lukejiang9020/solartrackers/imgs/basic_diagram.png

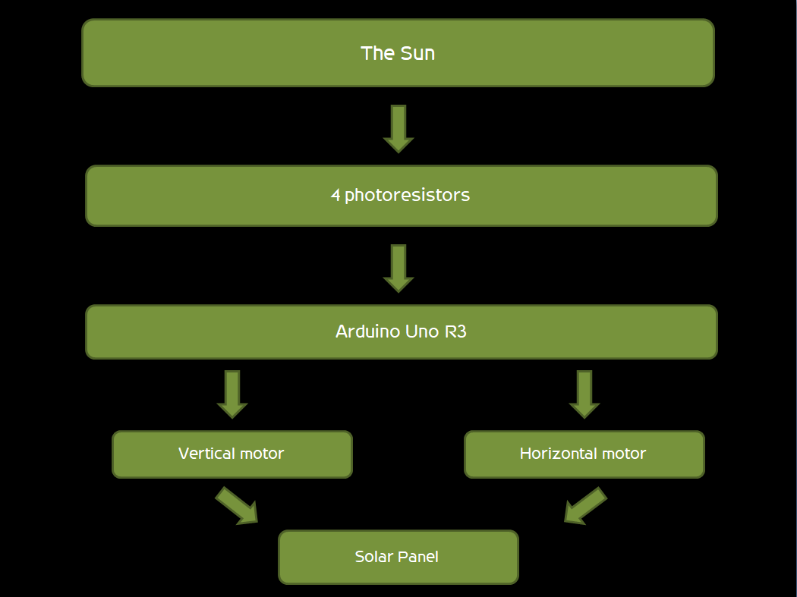
imgs/basic_diagram.png
