lukejiang9020/solartrackers/imgs/circuit_diagram.png

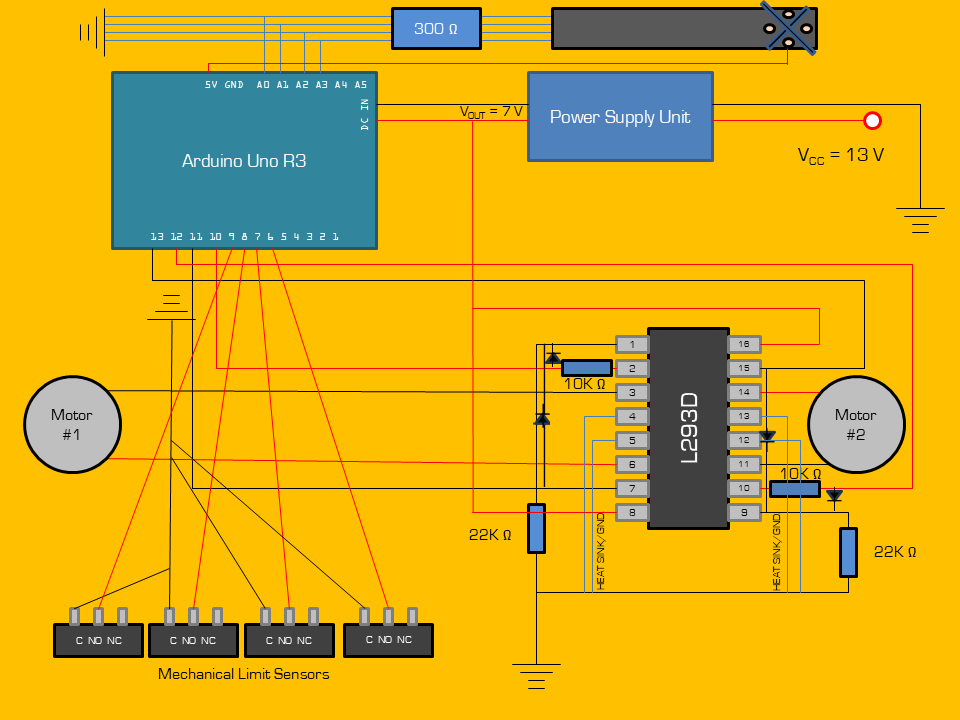
imgs/circuit_diagram.png
