lukejiang9020/solartrackers/imgs/enable disable pin.png

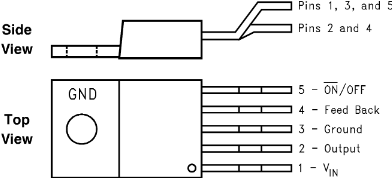
imgs/enable disable pin.png
