lukejiang9020/solartrackers/imgs/gimbal_crossview.png

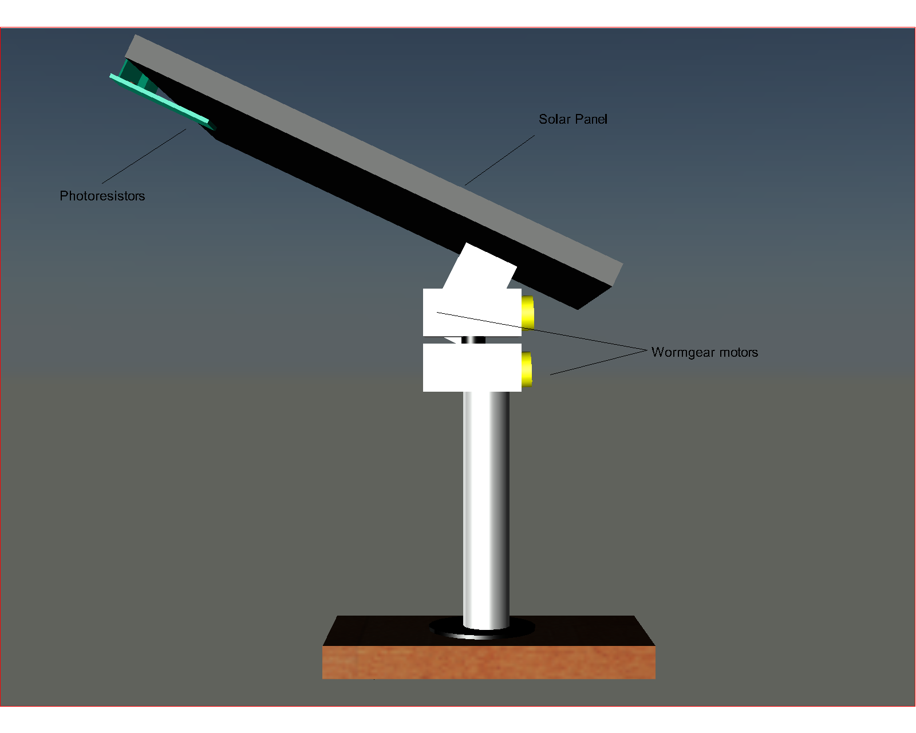
imgs/gimbal_crossview.png
