lukejiang9020/solartrackers/imgs/gimbal_isometric.png

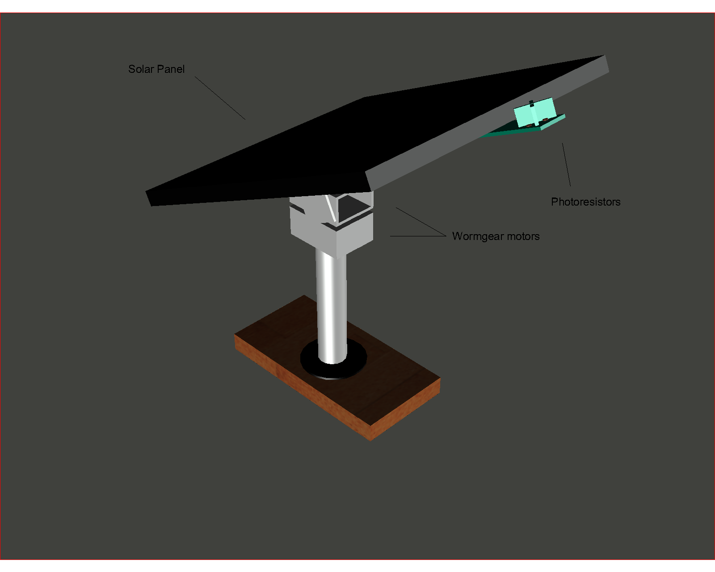
imgs/gimbal_isometric.png
