lukejiang9020/solartrackers/imgs/original_tracker.png

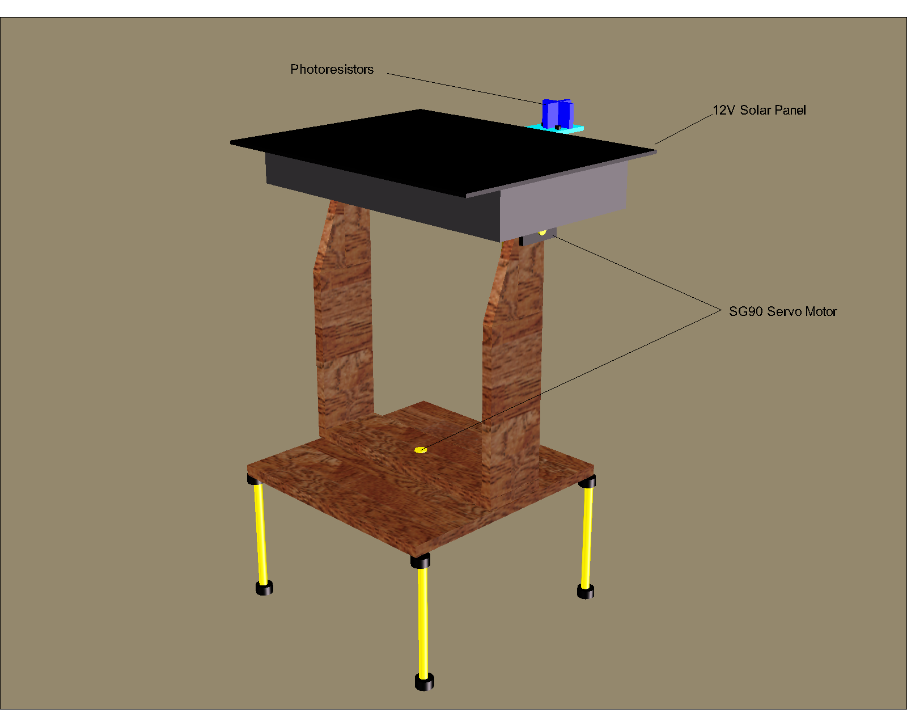
imgs/original_tracker.png
