lukejiang9020/solartrackers/imgs/schmitt trigger/schmitt trigger.001.jpeg

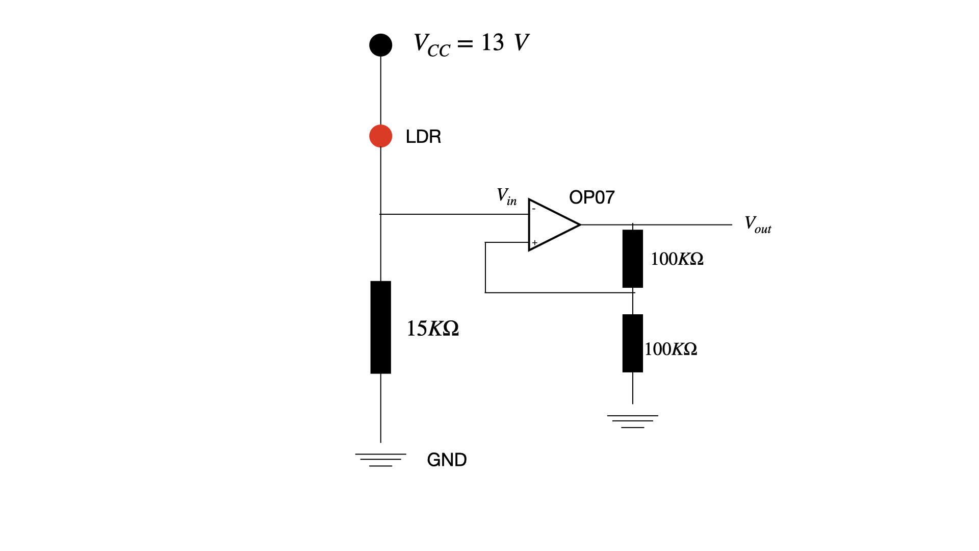
imgs/schmitt trigger/schmitt trigger.001.jpeg
