lukejiang9020/solartrackers/imgs/SolarPanel_alignment.png

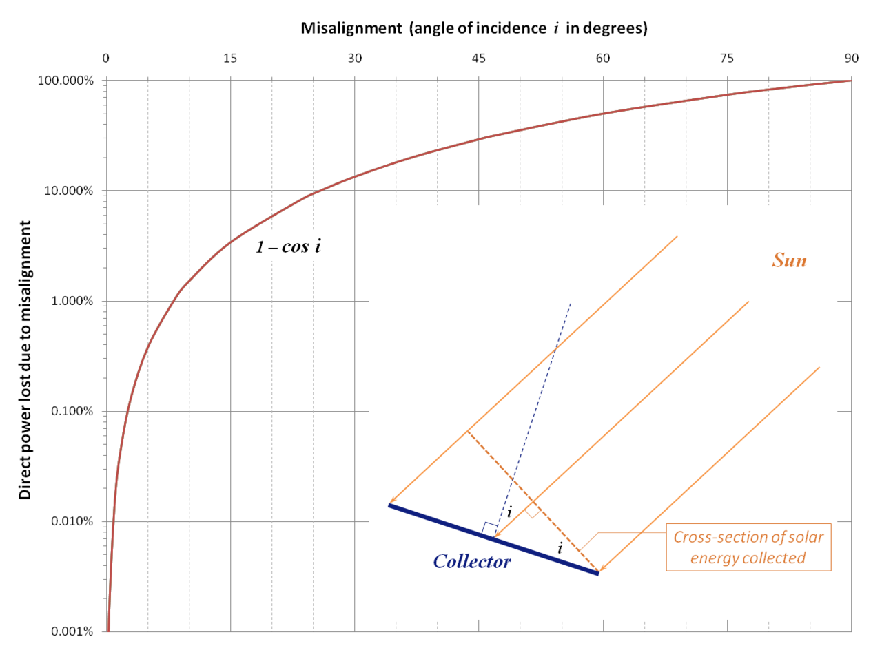
imgs/SolarPanel_alignment.png
